ossovskiy/Transcranial-neuromodulator/hardware/KiCad-project/Transcranial Neuro Modulator.kicad_sch

## KiCad design hardware/KiCad-project/Transcranial Neuro Modulator.kicad_sch (2026-09-26)

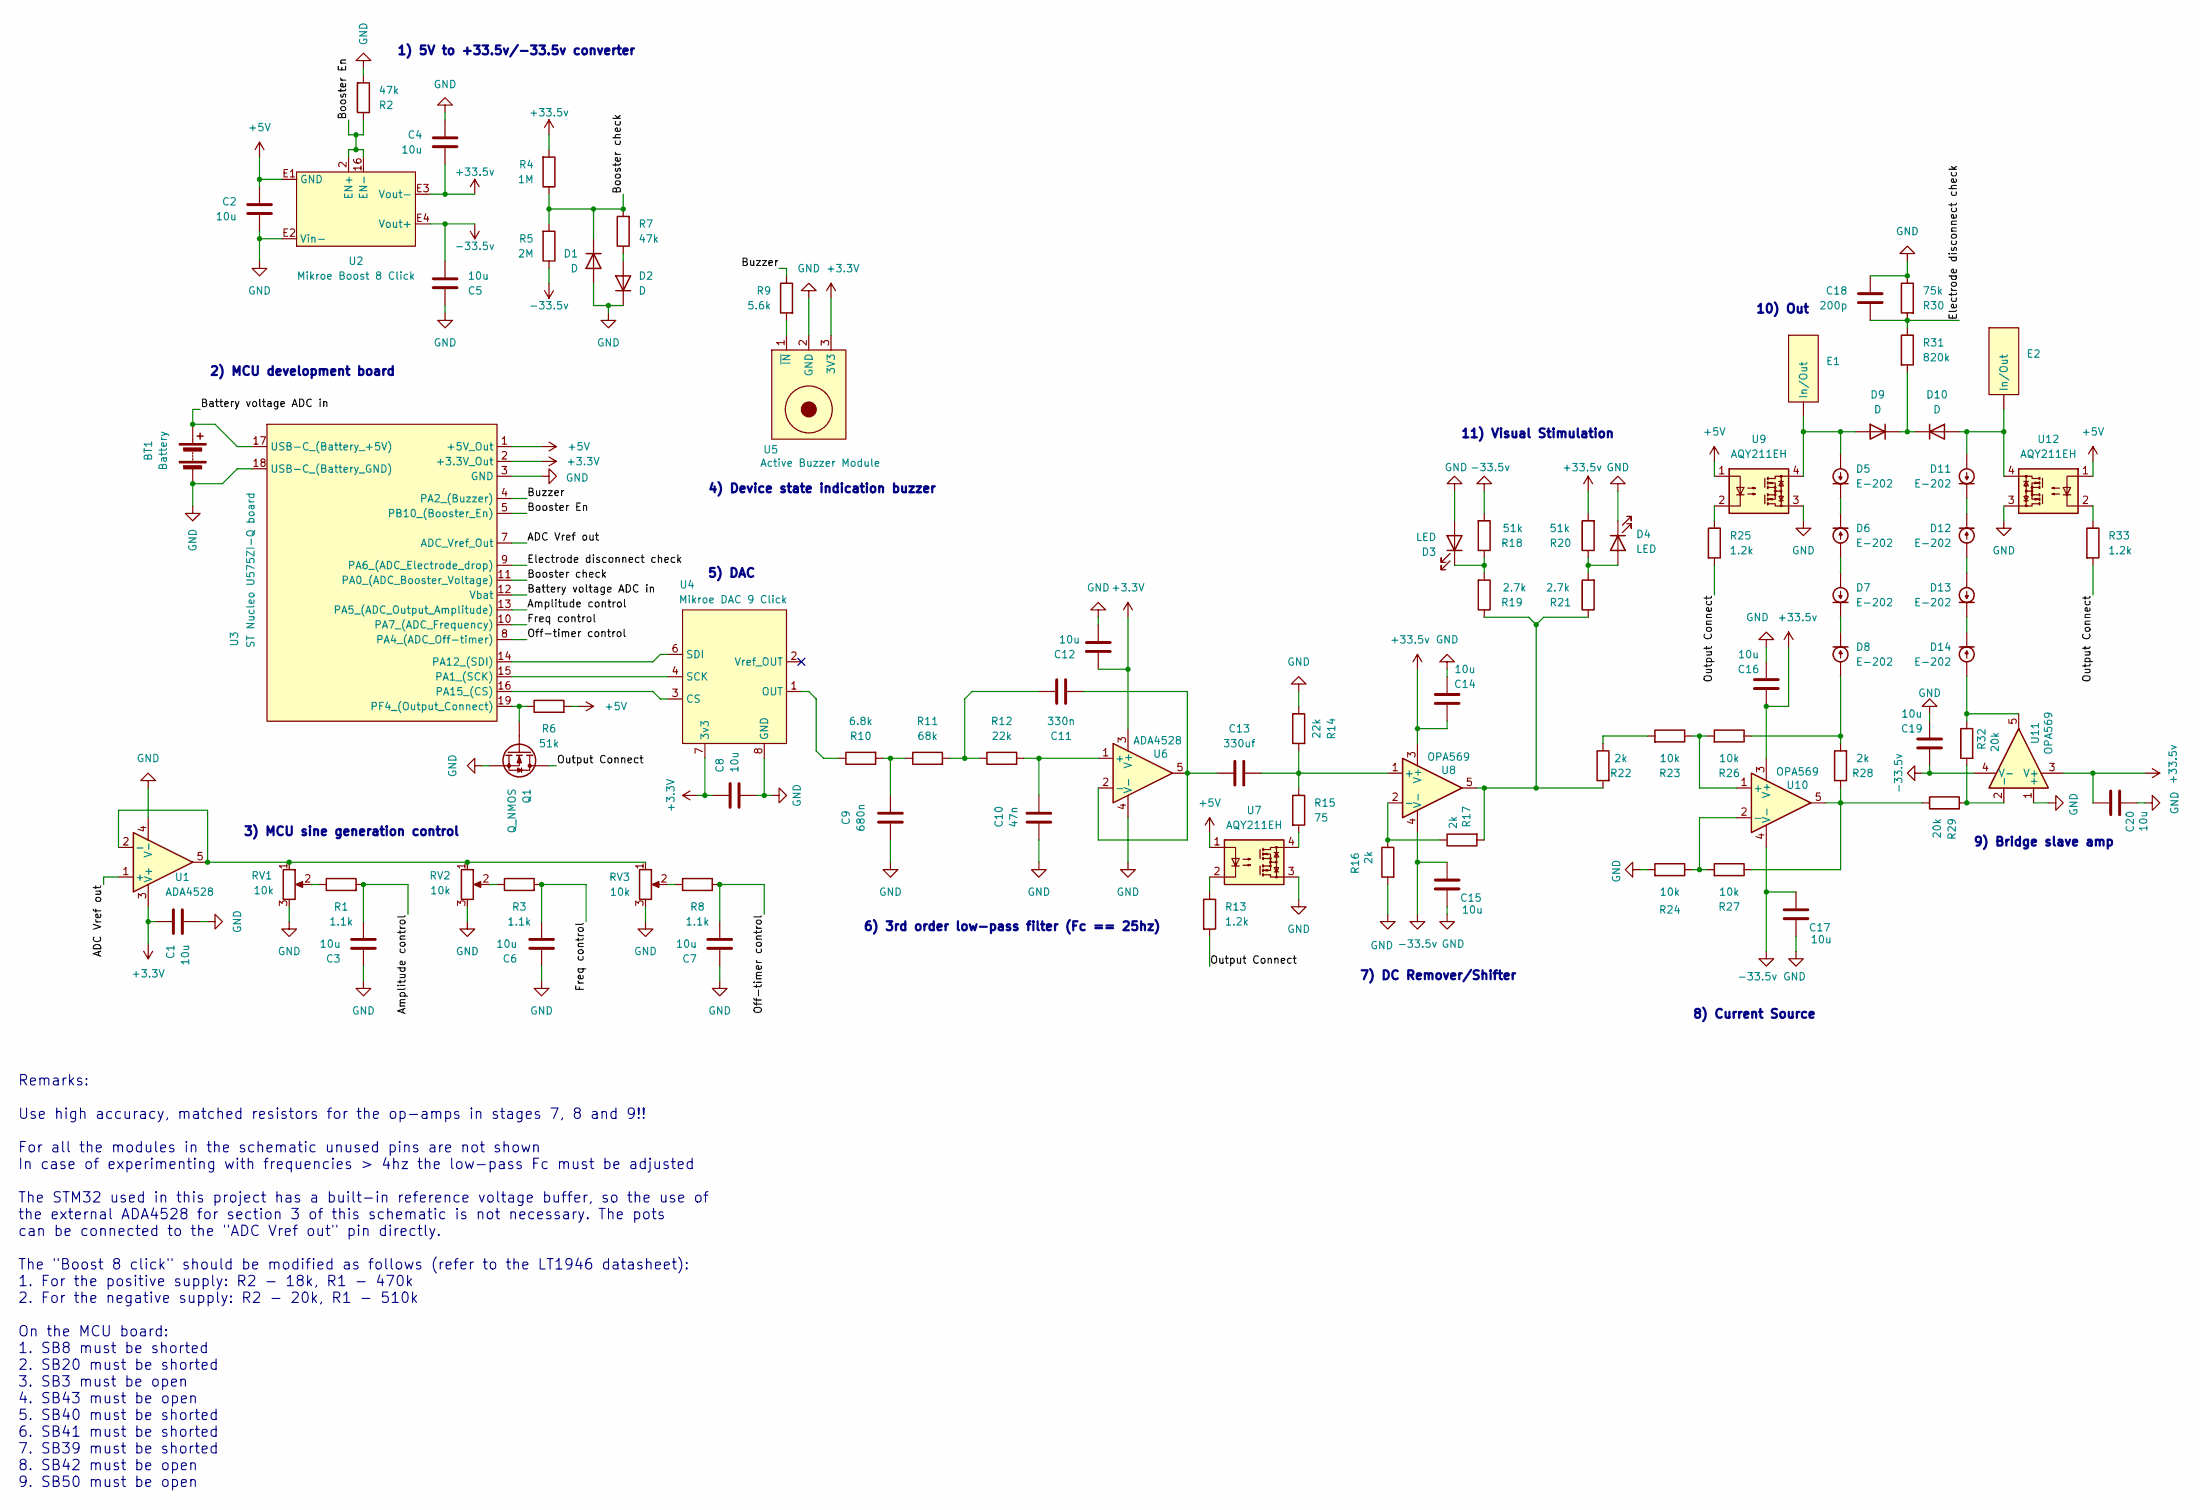
[picture p2: schematic Transcranial Neuro Modulator.kicad_sch]

Parts:
BT1: Battery
C1, C2, C3, C4, C5, C6, C7, C8, C12, C14, C15, C16, C17, C19, C20: 10u
C9: 680n
C10: 47n
C11: 330n
C13: 330uf
C18: 200p
D1, D2, D9, D10: D
D3, D4: LED
D5, D6, D7, D8, D11, D12, D13, D14: E-202
E1, E2: (no value)
Q1: Q_NMOS
R1, R3, R8: 1.1k
R2, R7: 47k
R4: 1M
R5: 2M
R6, R18, R20: 51k
R9: 5.6k
R10: 6.8k
R11: 68k
R12, R14: 22k
R13, R25, R33: 1.2k
R15: 75
R16, R17, R22, R28: 2k
R19, R21: 2.7k
R23, R24, R26, R27: 10k
R29, R32: 20k
R30: 75k
R31: 820k
RV1, RV2, RV3: 10k
U1, U6: ADA4528
U2: Mikroe Boost 8 Click
U3: ST Nucleo U575ZI-Q board
U4: Mikroe DAC 9 Click
U5: Active Buzzer Module
U7, U9, U12: AQY211EH; DIP-4_W7.62mm
U8, U10, U11: OPA569

Connections:
+3.3V: C1.1, C8.1, C12.1, U1.3 (V+), U3.2 (+3.3V_Out), U4.7 (3v3), U5.3 (3V3), U6.3 (V+)
+5V: C2.1, R6.2, U2.E1 (GND), U3.1 (+5V_Out), U7.1, U9.1, U12.1
+33.5v: C4.2, C14.1, C16.1, C20.1, R4.2, R20.2, U2.E3 (Vout-), U8.3 (V+), U10.3 (V+), U11.3 (V+)
-33.5v: C5.2, C15.1, C17.1, C19.1, R5.1, R18.2, U2.E4 (Vout+), U8.4 (V-), U10.4 (V-), U11.4 (V-)
ADC Vref out: U1.1 (+), U3.7 (ADC_Vref_Out)
Amplitude control: C3.2, R1.2, U3.13 (PA5_(ADC_Output_Amplitude))
Battery voltage ADC in: BT1.1 (+), U3.12 (Vbat), U3.17 (USB-C_(Battery_+5V))
Booster En: R2.1, U2.2 (EN+), U2.16 (EN-), U3.5 (PB10_(Booster_En))
Booster check: D1.1 (K), R4.1, R5.2, R7.2, U3.11 (PA0_(ADC_Booster_Voltage))
Buzzer: R9.1, U3.4 (PA2_(Buzzer))
Electrode disconnect check: C18.2, R30.2, R31.1, U3.9 (PA6_(ADC_Electrode_drop))
Freq control: C6.2, R3.2, U3.10 (PA7_(ADC_Frequency))
GND: BT1.2 (-), C1.2, C2.2, C3.1, C4.1, C5.1, C6.1, C7.1, C8.2, C9.2, C10.2, C12.2, C14.2, C15.2, C16.2, C17.2, C18.1, C19.2, C20.2, D1.2 (A), D2.1 (K), D3.2 (A), D4.1 (K), Q1.S, R2.2, R14.1, R16.2, R24.2, R30.1, RV1.3, RV2.3, RV3.3, U1.4 (V-), U2.E2 (Vin-), U3.3 (GND), U3.18 (USB-C_(Battery_GND)), U4.8 (GND), U5.2 (GND), U6.4 (V-), U7.3, U9.3, U11.1 (+), U12.3
unnamed: C9.1, R10.2, R11.1
unnamed: C10.1, R12.2, U6.1 (+)
unnamed: C11.1, R11.2, R12.1
unnamed: C11.2, C13.2, U6.2 (-), U6.5
unnamed: C13.1, R14.2, R15.1, U8.1 (+)
unnamed: D2.2 (A), R7.1
unnamed: D3.1 (K), R18.1, R19.2
unnamed: D4.2 (A), R20.1, R21.2
unnamed: D5.1 (K), D6.1 (K)
unnamed: D5.2 (A), D9.2 (A), E1., U9.4
unnamed: D6.2 (A), D7.2 (A)
unnamed: D7.1 (K), D8.1 (K)
unnamed: D8.2 (A), R26.1, R28.2
unnamed: D9.1 (K), D10.1 (K), R31.2
unnamed: D10.2 (A), D11.2 (A), E2., U12.4
unnamed: D11.1 (K), D12.1 (K)
unnamed: D12.2 (A), D13.2 (A)
unnamed: D13.1 (K), D14.1 (K)
unnamed: D14.2 (A), R32.1, U11.5
unnamed: Q1.G, R6.1, U3.19 (PF4_(Output_Connect))
unnamed: R1.1, RV1.2
unnamed: R3.1, RV2.2
unnamed: R8.1, RV3.2
unnamed: R9.2, U5.1 (~IN)
unnamed: R10.1, U4.1 (OUT)
unnamed: R13.1, U7.2
unnamed: R15.2, U7.4
unnamed: R16.1, R17.1, U8.2 (-)
unnamed: R17.2, R19.1, R21.1, R22.2, U8.5
unnamed: R22.1, R23.2
unnamed: R23.1, R26.2, U10.1 (+)
unnamed: R24.1, R27.2, U10.2 (-)
unnamed: R25.1, U9.2
unnamed: R27.1, R28.1, R29.1, U10.5
unnamed: R29.2, R32.2, U11.2 (-)
unnamed: R33.1, U12.2
unnamed: RV1.1, RV2.1, RV3.1, U1.2 (-), U1.5
unnamed: U3.14 (PA12_(SDI)), U4.6 (SDI)
unnamed: U3.15 (PA1_(SCK)), U4.4 (SCK)
unnamed: U3.16 (PA15_(CS)), U4.3 (CS)
Off-timer control: C7.2, R8.2, U3.8 (PA4_(ADC_Off-timer))
Output Connect: Q1.D, R13.2, R25.2, R33.2

Notes on the sheet:
7) DC Remover/Shifter
2) MCU development board
Remarks: Use high accuracy, matched resistors for the op-amps in stages 7, 8 and 9!! For all the modules in the schematic unused pins are not shown In case of experimenting with frequencies > 4hz the low-pass Fc must be adjusted The STM32 used in this project has a built-in reference voltage buffer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
11) Visual Stimulation
1) 5V to +33.5v/-33.5v converter
10) Out
6) 3rd order low-pass filter (Fc == 25hz)
4) Device state indication buzzer
9) Bridge slave amp
5) DAC
8) Current Source
3) MCU sine generation control
